cedwies/SpatialMouse/Weekly Reports/Figures/MouseButtons2.jpeg

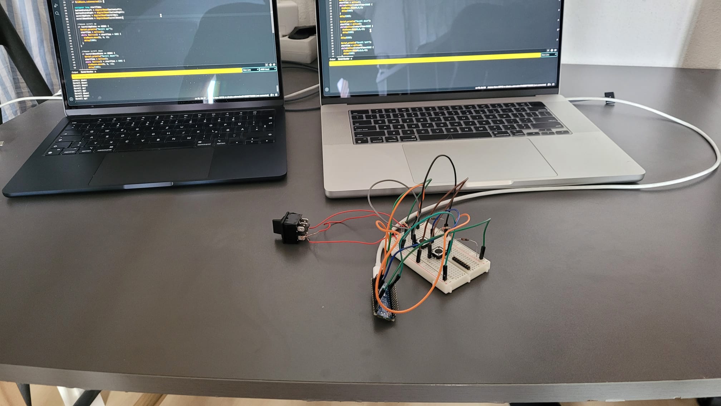
Weekly Reports/Figures/MouseButtons2.jpeg
